LEDswarm/NeoPixelRing/openscad/main.scad

include <lib/round_anything/polyround.scad>;

include <config.scad>;

include <led.scad>;
include <board/board.scad>;

BoardPcb();
